ftessari23/GimbalPaper/90154A273_External Retaining Ring.SLDPRT

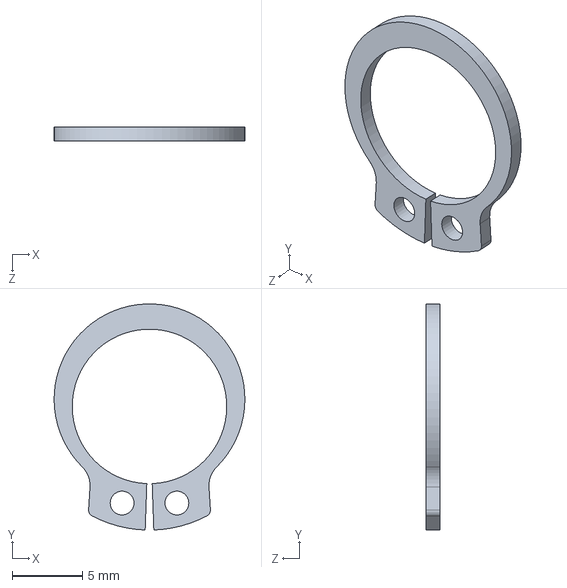
[picture p15: CAD file, 2025-08-29]
90154A273_External Retaining Ring.SLDPRT
13.6 x 16.1 x 1.00 mm
