ftessari23/GimbalPaper/60715K111_One-Piece Steel Thrust Ball Bearing.SLDPRT

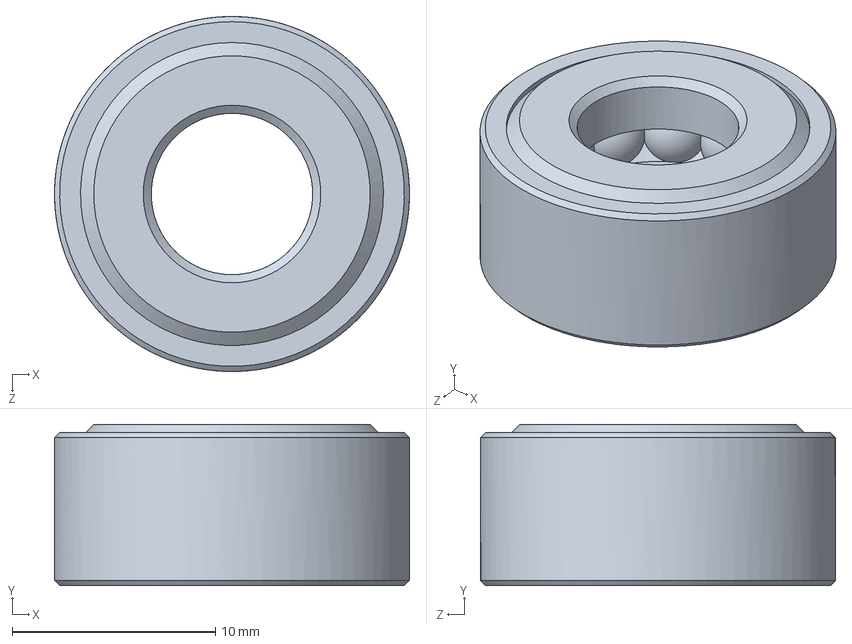
[picture p16: CAD file, 2025-08-29]
60715K111_One-Piece Steel Thrust Ball Bearing.SLDPRT
17.5 x 7.94 x 17.5 mm
